madworm/8x8_RGB_LED_Matrix_Controller/gerber_files/PNGs/8x8_rgb_matrix-V3_04__front.png

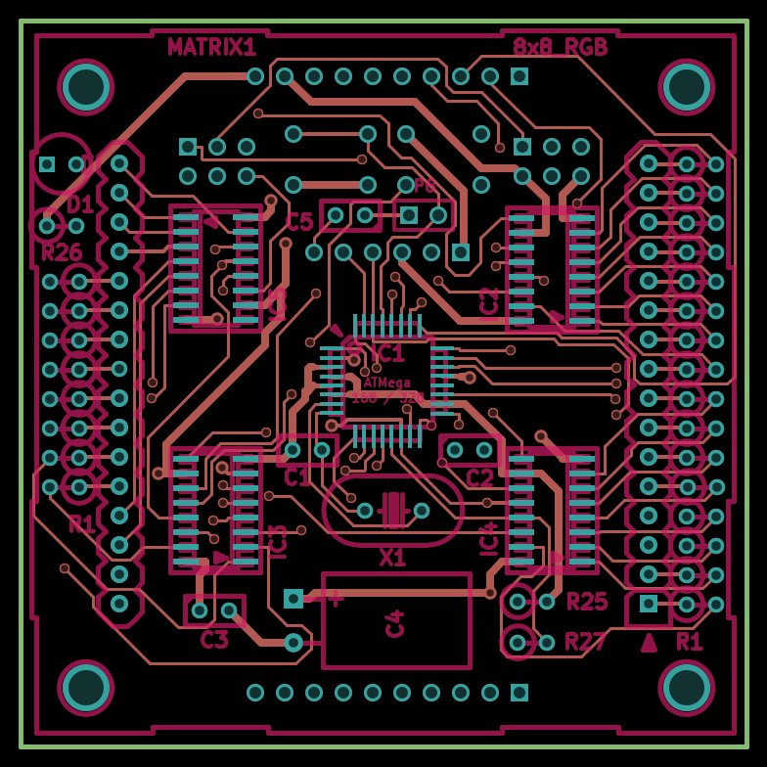
gerber_files/PNGs/8x8_rgb_matrix-V3_04__front.png
